cnvogelg/es_buddy/blob.cpp

#include "audio/analyze_avgarray.cpp"
#include "audio/analyze_minmax.cpp"

#include "tinyui/scene_renderer.cpp"
#include "tinyui/scene.cpp"
#include "tinyui/stage.cpp"

#include "widgets/text_widget.cpp"
#include "widgets/scope_widget.cpp"
#include "widgets/bar_widget.cpp"
#include "widgets/spectrum_widget.cpp"
