cnvogelg/es_buddy/tinyui/event.h

#ifndef EVENT_H
#define EVENT_H

#include <Encoder.h>
#include <Bounce.h>

enum class EventType {
    INC_VALUE,
    DEC_VALUE,
    BUTTON_DOWN,
    BUTTON_UP,
    BUTTON_UP_LONG,
    BUTTON_UP_EXTRA_LONG
};

struct Event {
    EventType  type;
    int        value;
};

class EventSource {
public:
    virtual bool pollEvent(Event &e) = 0;
};

#endif
